Jean-K3/Gate_O_matix/Kicad/My_library/Mes_modèles_3D/IC_Sockets/DIP-6 W7.62mm IC with Socket.stp

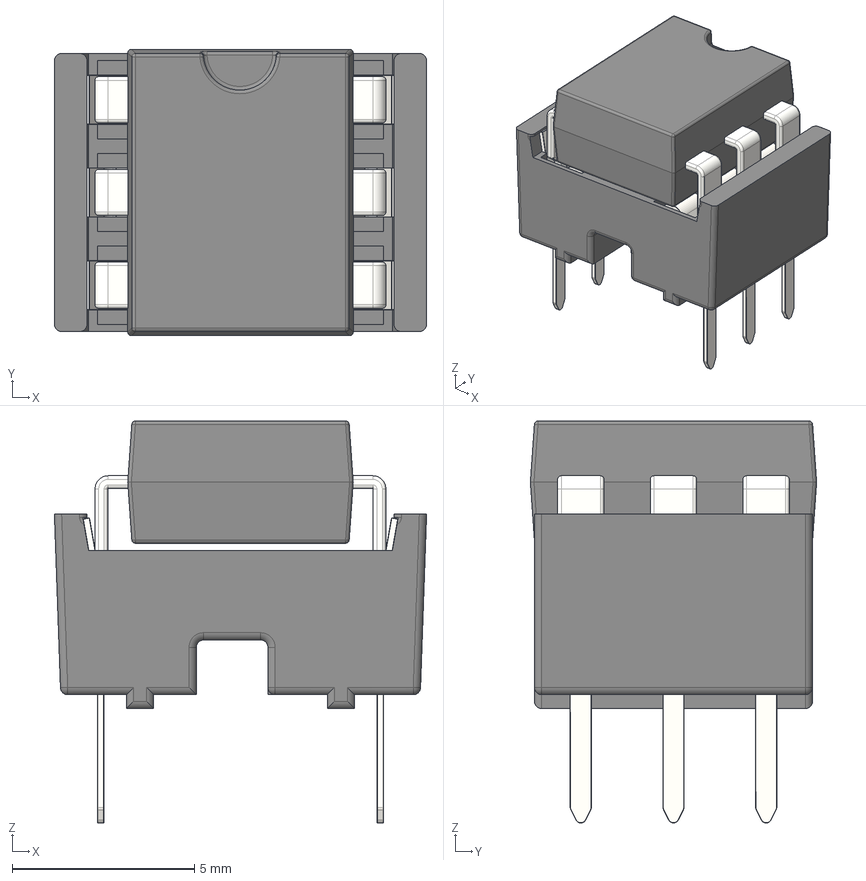
[picture p21: CAD file, 2021-02-17]
Kicad/My_library/Mes_modèles_3D/IC_Sockets/DIP-6 W7.62mm IC with Socket.stp
10.2 x 7.85 x 11.0 mm
Stamped Dual Wipe Contact for DIP Sockets x 6
Body DIP-6 P7.62mm Socket
IC Beinchen x 6
DIP-6 W7.62
