Jean-K3/Gate_O_matix/Kicad/My_library/Mes_modèles_3D/bh-connector-set-1.snapshot.1/BH-40R.STEP

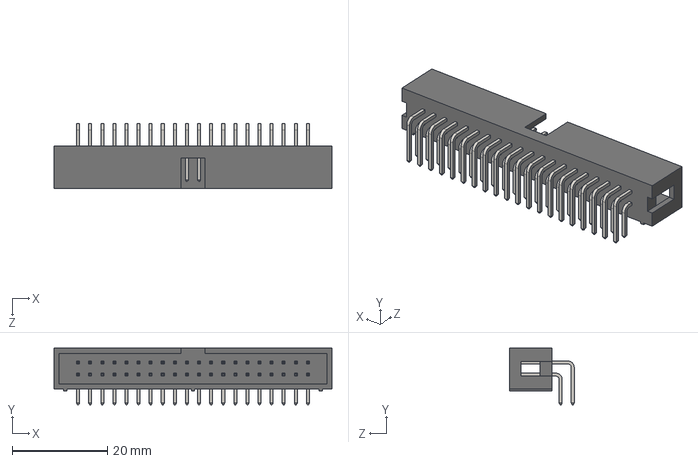
[picture p22: CAD file, 2021-02-17]
Kicad/My_library/Mes_modèles_3D/bh-connector-set-1.snapshot.1/BH-40R.STEP
58.4 x 11.9 x 13.6 mm
