Jean-K3/Gate_O_matix/Kicad/My_library/Mes_modèles_3D/IC_Sockets/DIP-20 W7.62mm IC with Socket.stp

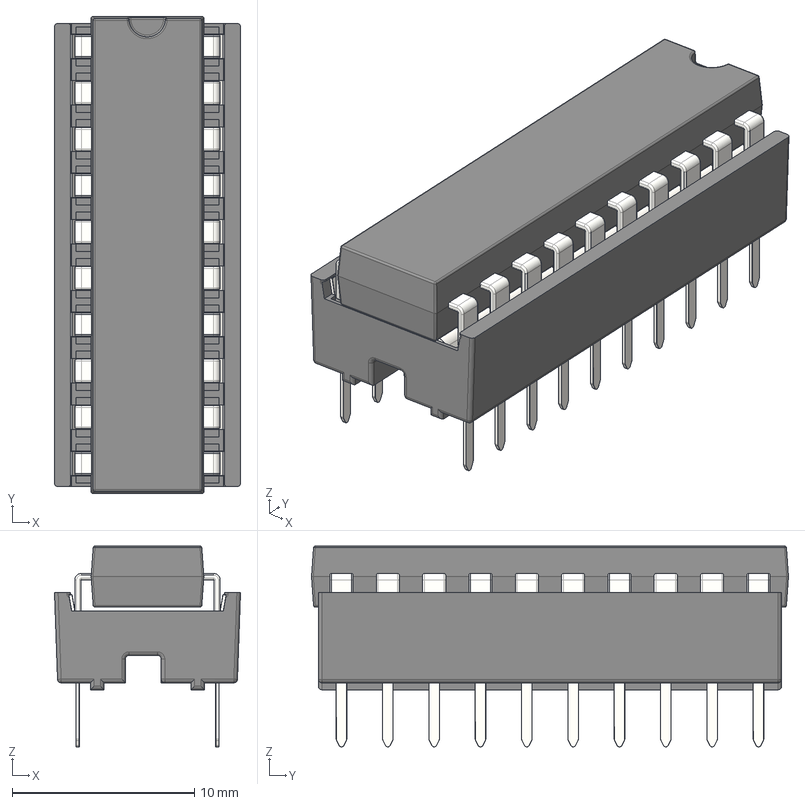
[picture p23: CAD file, 2021-02-17]
Kicad/My_library/Mes_modèles_3D/IC_Sockets/DIP-20 W7.62mm IC with Socket.stp
10.2 x 26.1 x 11.0 mm
Stamped Dual Wipe Contact for DIP Sockets x 20
Body DIP-20 P7.62mm Socket
IC Beinchen x 20
DIP-20 W7.62
