Jean-K3/Gate_O_matix/Kicad/My_library/Mes_modèles_3D/bh-connector-set-1.snapshot.1/BH-34R.STEP

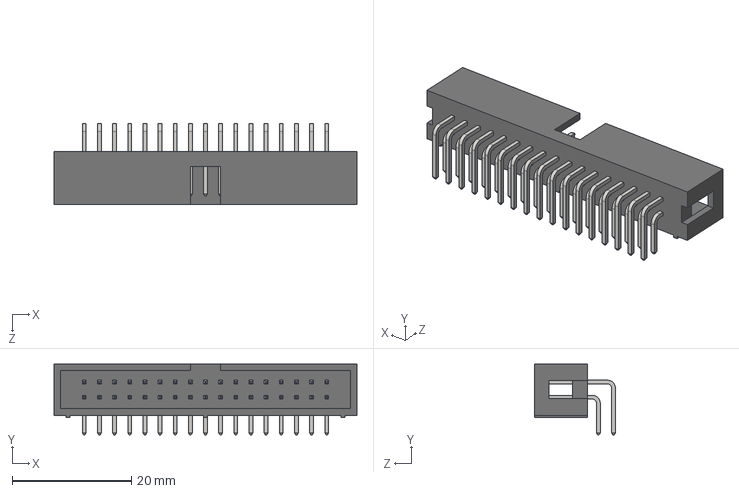
[picture p24: CAD file, 2021-02-17]
Kicad/My_library/Mes_modèles_3D/bh-connector-set-1.snapshot.1/BH-34R.STEP
50.8 x 11.9 x 13.6 mm
