Jean-K3/Gate_O_matix/Kicad/My_library/Mes_modèles_3D/bh-connector-set-1.snapshot.1/BH-26R.STEP

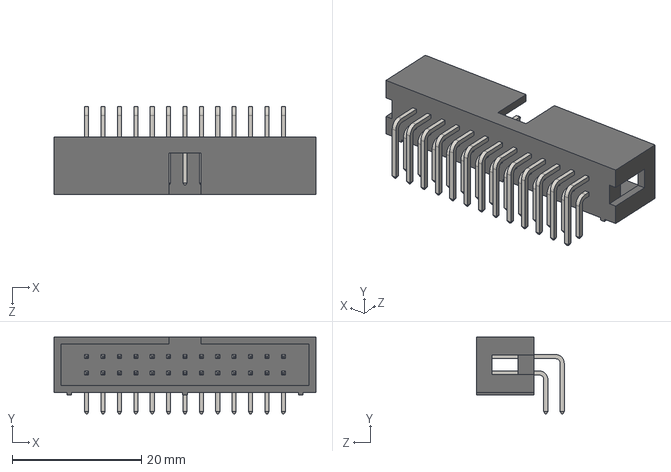
[picture p26: CAD file, 2021-02-17]
Kicad/My_library/Mes_modèles_3D/bh-connector-set-1.snapshot.1/BH-26R.STEP
40.6 x 11.9 x 13.6 mm
