Jean-K3/Gate_O_matix/Kicad/My_library/Mes_modèles_3D/IC_Sockets/DIP-4 W7.62mm IC with Socket.stp

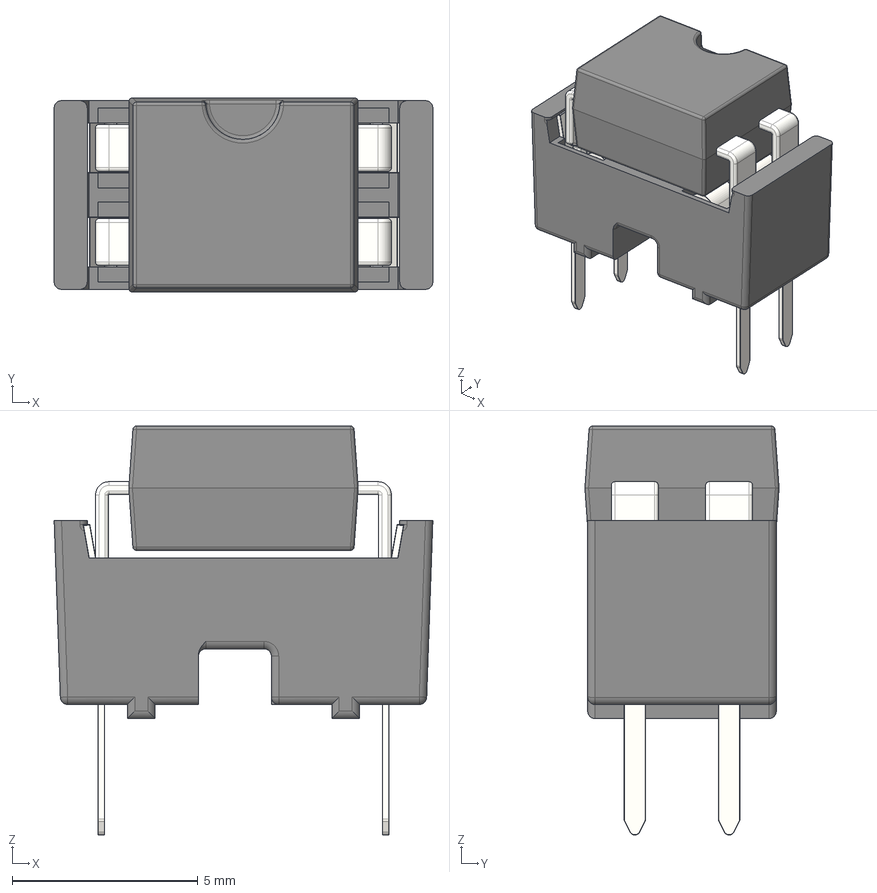
[picture p28: CAD file, 2021-02-17]
Kicad/My_library/Mes_modèles_3D/IC_Sockets/DIP-4 W7.62mm IC with Socket.stp
10.2 x 5.23 x 11.0 mm
Stamped Dual Wipe Contact for DIP Sockets x 4
Body DIP-4 P7.62mm Socket
IC Beinchen x 4
DIP-4 W7.62
