Jean-K3/Gate_O_matix/Kicad/My_library/Mes_modèles_3D/bh-connector-set-1.snapshot.1/BH-50.STEP

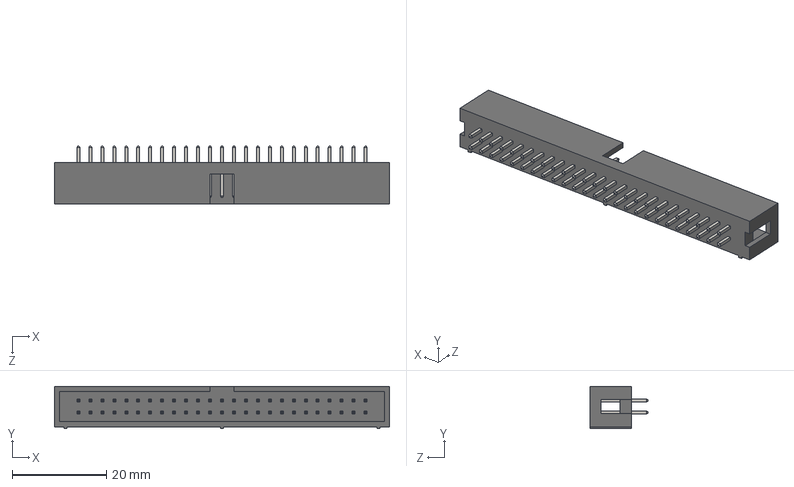
[picture p29: CAD file, 2021-02-17]
Kicad/My_library/Mes_modèles_3D/bh-connector-set-1.snapshot.1/BH-50.STEP
71.1 x 9.00 x 12.4 mm
