Jean-K3/Gate_O_matix/Kicad/My_library/Mes_modèles_3D/Encoders/EC11B-SW-Vert-15K-blue.step

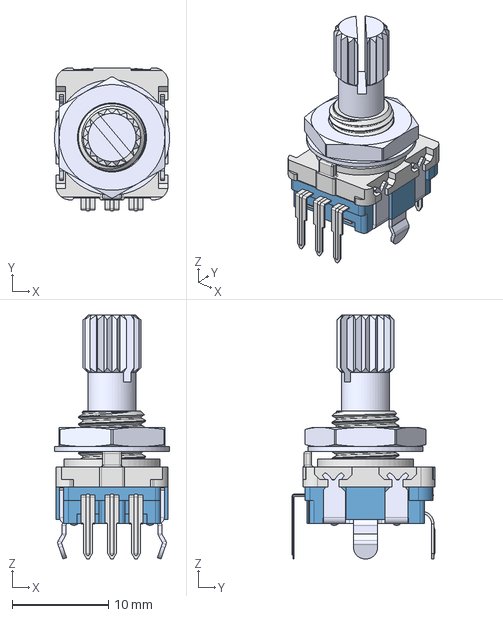
[picture p30: CAD file, 2021-02-17]
Kicad/My_library/Mes_modèles_3D/Encoders/EC11B-SW-Vert-15K-blue.step
12.0 x 14.9 x 25.4 mm
