Jean-K3/Gate_O_matix/Kicad/My_library/Mes_modèles_3D/IC_Sockets/DIP-5 W7.62mm IC with Socket.stp

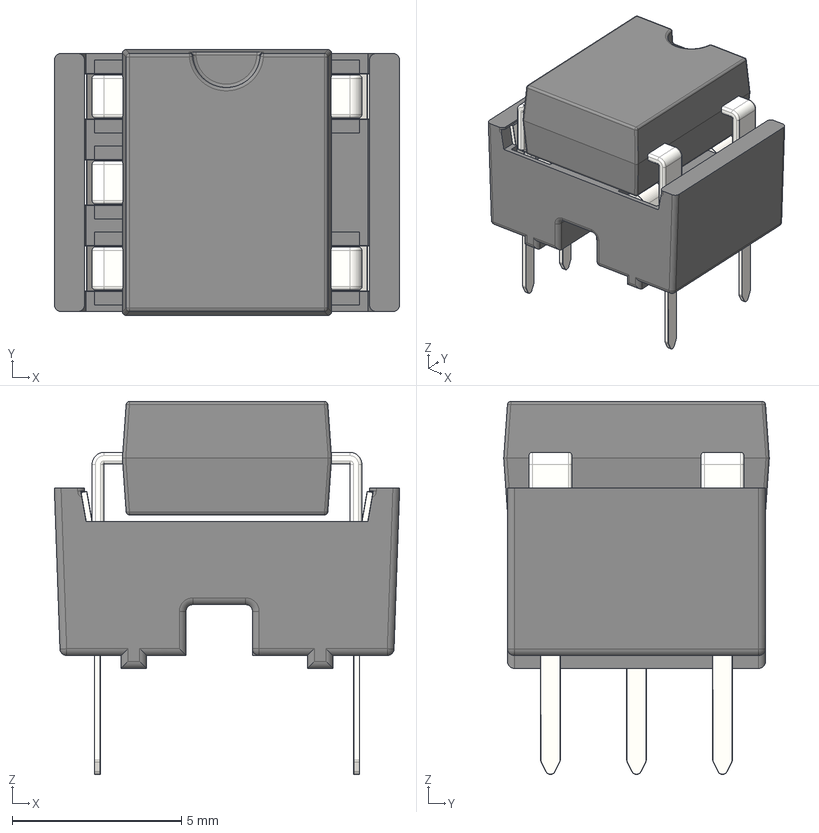
[picture p33: CAD file, 2021-02-17]
Kicad/My_library/Mes_modèles_3D/IC_Sockets/DIP-5 W7.62mm IC with Socket.stp
10.2 x 7.85 x 11.0 mm
Stamped Dual Wipe Contact for DIP Sockets x 5
IC Beinchen x 5
DIP-5 W7.62
Body DIP-5 P7.62mm Socket
