Jean-K3/Gate_O_matix/Kicad/My_library/Mes_modèles_3D/IC_Sockets/DIP-28 W7.62mm IC with Socket.stp

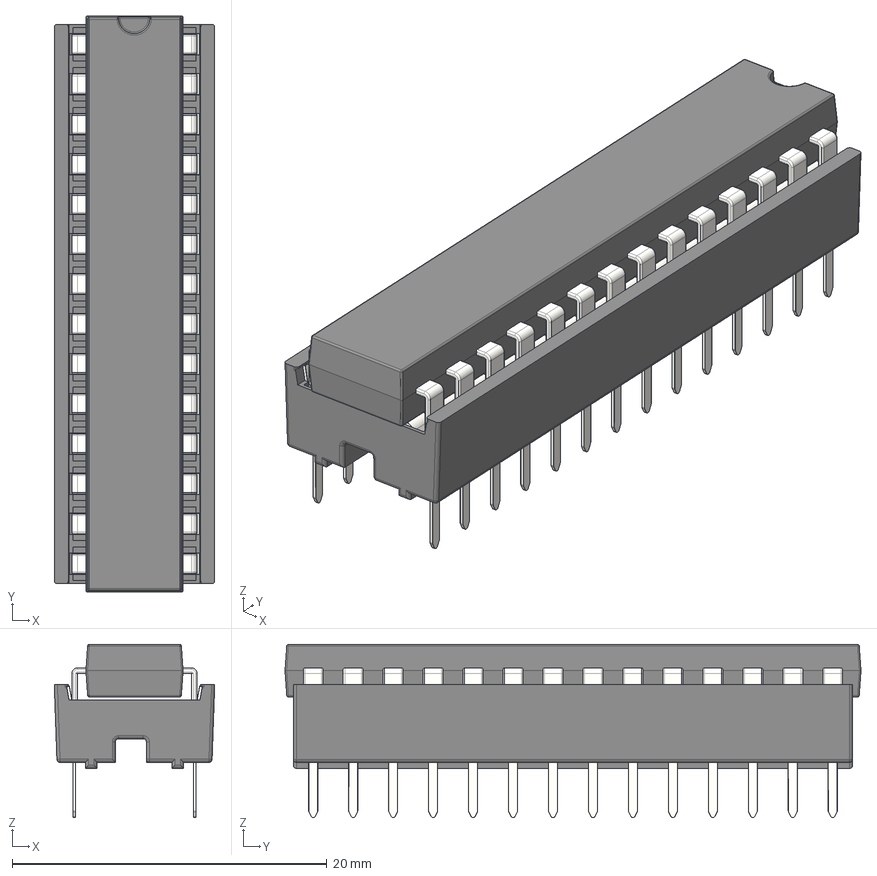
[picture p35: CAD file, 2021-02-17]
Kicad/My_library/Mes_modèles_3D/IC_Sockets/DIP-28 W7.62mm IC with Socket.stp
10.2 x 36.6 x 11.0 mm
Stamped Dual Wipe Contact for DIP Sockets x 28
Body DIP-28 P7.62mm Socket
IC Beinchen x 28
DIP-28 W7.62
