Jean-K3/Gate_O_matix/Kicad/My_library/Mes_modèles_3D/Encoders/EC11B-SW-Vert-25K-green.step

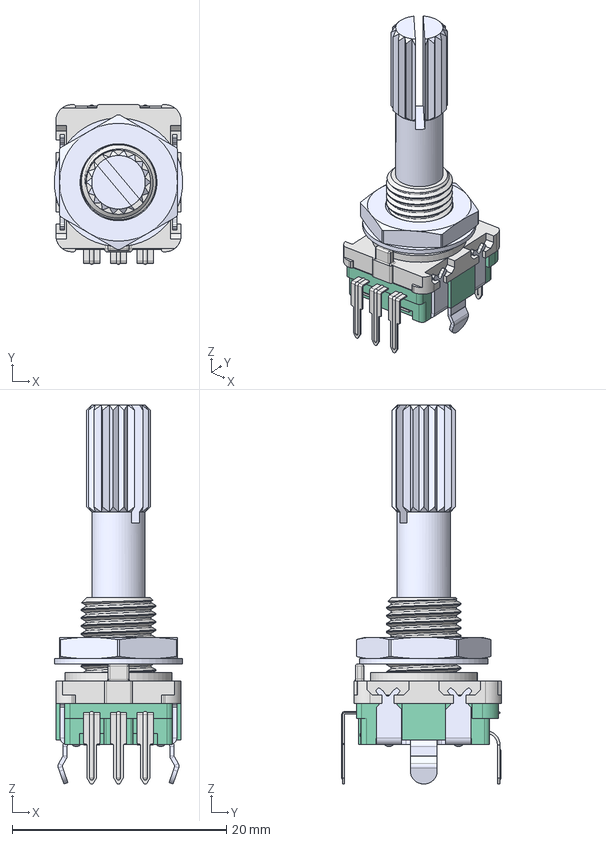
[picture p37: CAD file, 2021-02-17]
Kicad/My_library/Mes_modèles_3D/Encoders/EC11B-SW-Vert-25K-green.step
12.0 x 14.9 x 35.4 mm
