Jean-K3/Gate_O_matix/Kicad/My_library/Mes_modèles_3D/IC_Sockets/DIP-8 W7.62mm IC with Socket.stp

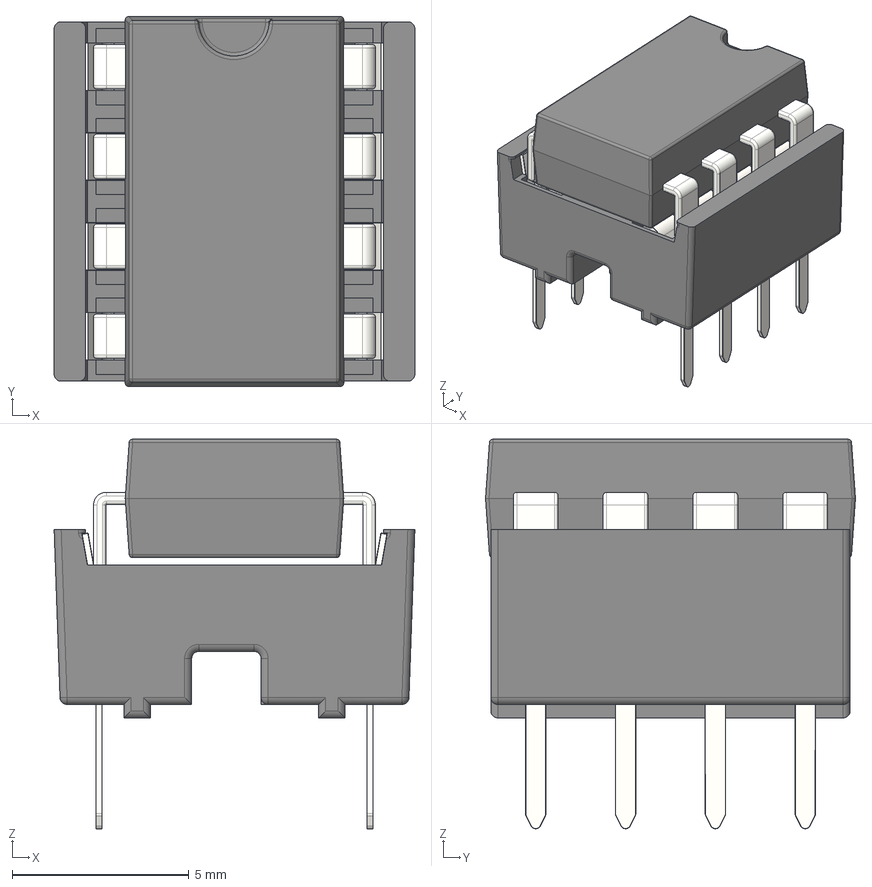
[picture p38: CAD file, 2021-02-17]
Kicad/My_library/Mes_modèles_3D/IC_Sockets/DIP-8 W7.62mm IC with Socket.stp
10.2 x 10.5 x 11.0 mm
Stamped Dual Wipe Contact for DIP Sockets x 8
Body DIP-8 P7.62mm Socket
IC Beinchen x 8
DIP-8 W7.62
