Jean-K3/Gate_O_matix/Kicad/My_library/Mes_modèles_3D/IC_Sockets/DIP-22 W7.62mm IC with Socket.stp

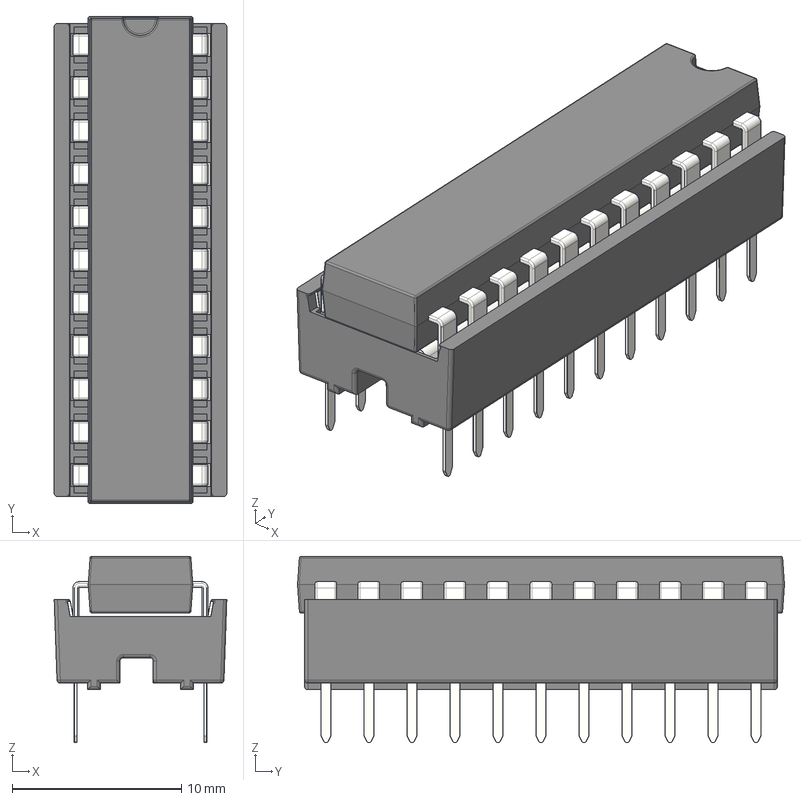
[picture p40: CAD file, 2021-02-17]
Kicad/My_library/Mes_modèles_3D/IC_Sockets/DIP-22 W7.62mm IC with Socket.stp
10.2 x 28.8 x 11.0 mm
Stamped Dual Wipe Contact for DIP Sockets x 22
Body DIP-22 P7.62mm Socket
IC Beinchen x 22
DIP-22 W7.62
