Jean-K3/Gate_O_matix/Kicad/My_library/Mes_modèles_3D/Encoders/EC11B-SW-Vert-20R-blue.step

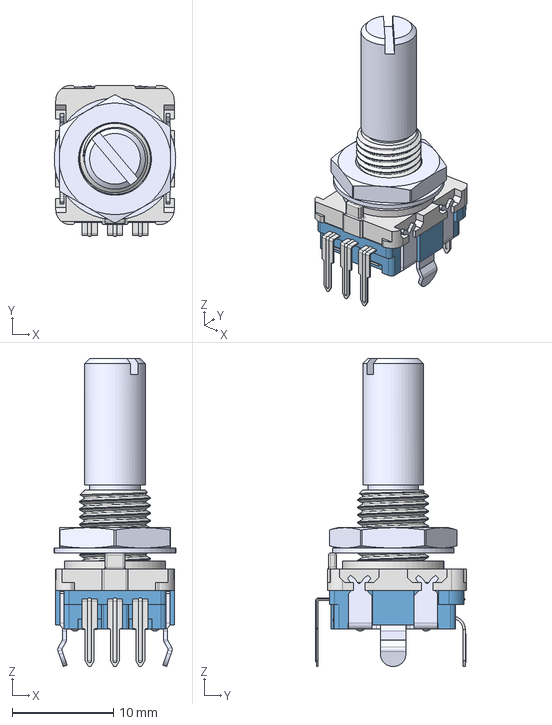
[picture p42: CAD file, 2021-02-17]
Kicad/My_library/Mes_modèles_3D/Encoders/EC11B-SW-Vert-20R-blue.step
12.0 x 14.9 x 30.4 mm
