Jean-K3/Gate_O_matix/Kicad/My_library/Mes_modèles_3D/IC_Sockets/DIP-12 W7.62mm IC with Socket.stp

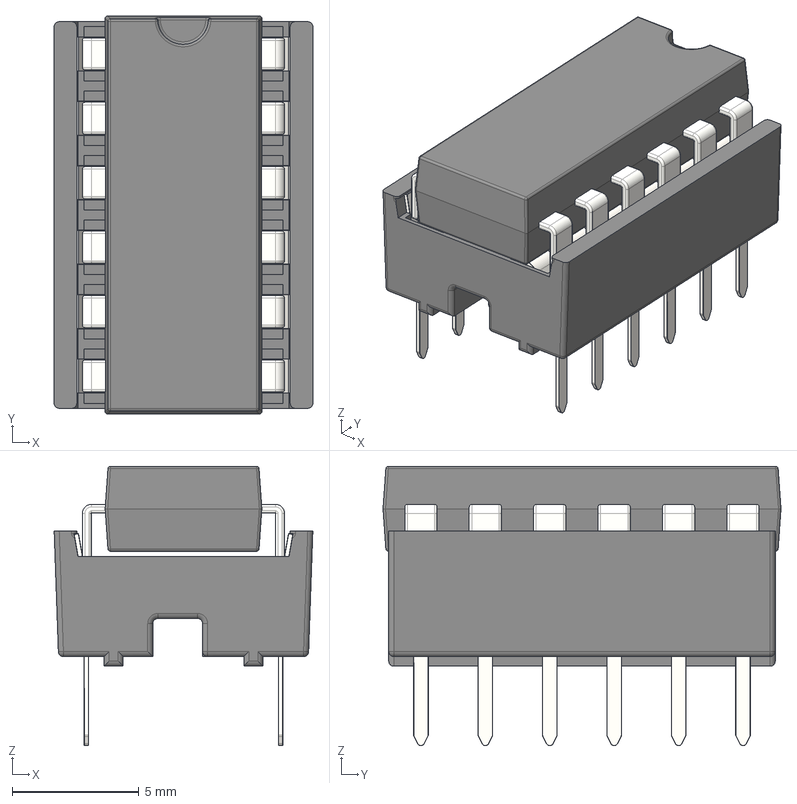
[picture p43: CAD file, 2021-02-17]
Kicad/My_library/Mes_modèles_3D/IC_Sockets/DIP-12 W7.62mm IC with Socket.stp
10.2 x 15.7 x 11.0 mm
Stamped Dual Wipe Contact for DIP Sockets x 12
Body DIP-12 P7.62mm Socket
IC Beinchen x 12
DIP-12 W7.62
