Jean-K3/Gate_O_matix/Kicad/My_library/Mes_modèles_3D/IC_Sockets/DIP-16 W7.62mm IC with Socket.stp

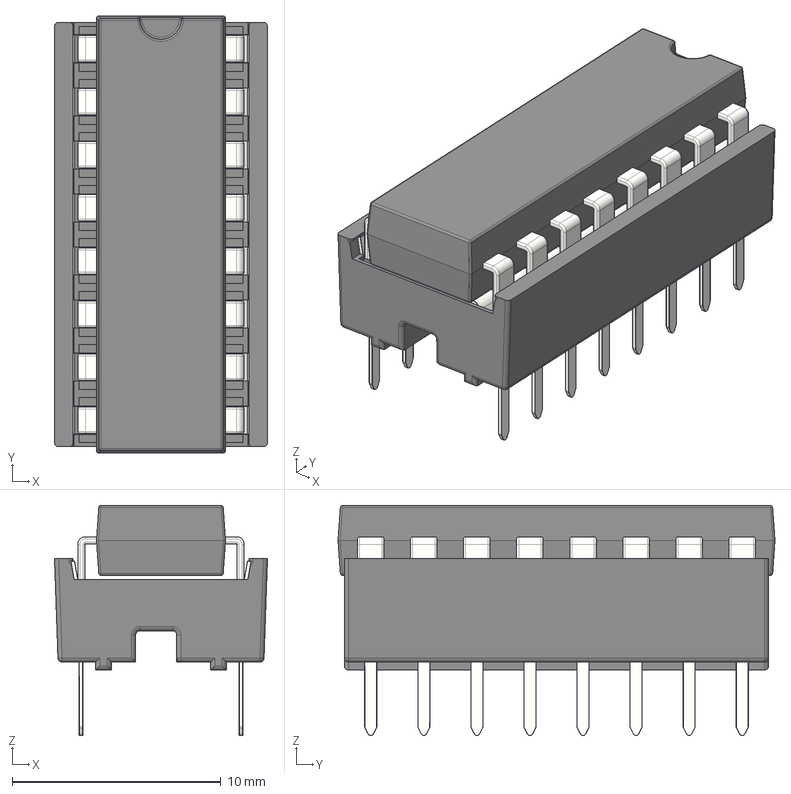
[picture p45: CAD file, 2021-02-17]
Kicad/My_library/Mes_modèles_3D/IC_Sockets/DIP-16 W7.62mm IC with Socket.stp
10.2 x 20.9 x 11.0 mm
Stamped Dual Wipe Contact for DIP Sockets x 16
Body DIP-16 P7.62mm Socket
IC Beinchen x 16
DIP-16 W7.62
